profdc9/PicoTheremin/MCTheremin/waves.cpp

#include "waves.h"
const unsigned short sinewave[4096] = {4095,4094,4094,4094,4094,4094,4094,4094,4094,4094,4094,4094,4094,4094,4094,4094,4094,4094,4094,4094,4094,4093,4093,4093,4093,4093,4093,4093,4093,4092,4092,4092,4092,4092,4092,4092,4091,4091,4091,4091,4091,4090,4090,4090,4090,4090,4089,4089,4089,4089,4088,4088,4088,4088,4087,4087,4087,4087,4086,4086,4086,4086,4085,4085,4085,4084,4084,4084,4083,4083,4083,4082,4082,4082,4081,4081,4081,4080,4080,4079,4079,4079,4078,4078,4078,4077,4077,4076,4076,4075,4075,4075,4074,4074,4073,4073,4072,4072,4071,4071,4070,4070,4069,4069,4068,4068,4067,4067,4066,4066,4065,4065,4064,4064,4063,4063,4062,4062,4061,4060,4060,4059,4059,4058,4058,4057,4056,4056,4055,4055,4054,4053,4053,4052,4051,4051,4050,4049,4049,4048,4047,4047,4046,4045,4045,4044,4043,4043,4042,4041,4041,4040,4039,4038,4038,4037,4036,4035,4035,4034,4033,4032,4032,4031,4030,4029,4028,4028,4027,4026,4025,4024,4024,4023,4022,4021,4020,4019,4019,4018,4017,4016,4015,4014,4013,4013,4012,4011,4010,4009,4008,4007,4006,4005,4005,4004,4003,4002,4001,4000,3999,3998,3997,3996,3995,3994,3993,3992,3991,3990,3989,3988,3987,3986,3985,3984,3983,3982,3981,3980,3979,3978,3977,3976,3975,3974,3973,3972,3971,3969,3968,3967,3966,3965,3964,3963,3962,3961,3960,3958,3957,3956,3955,3954,3953,3952,3950,3949,3948,3947,3946,3945,3943,3942,3941,3940,3939,3937,3936,3935,3934,3933,3931,3930,3929,3928,3926,3925,3924,3923,3921,3920,3919,3918,3916,3915,3914,3912,3911,3910,3909,3907,3906,3905,3903,3902,3901,3899,3898,3897,3895,3894,3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
056,4056,4057,4058,4058,4059,4059,4060,4060,4061,4062,4062,4063,4063,4064,4064,4065,4065,4066,4066,4067,4067,4068,4068,4069,4069,4070,4070,4071,4071,4072,4072,4073,4073,4074,4074,4075,4075,4075,4076,4076,4077,4077,4078,4078,4078,4079,4079,4079,4080,4080,4081,4081,4081,4082,4082,4082,4083,4083,4083,4084,4084,4084,4085,4085,4085,4086,4086,4086,4086,4087,4087,4087,4087,4088,4088,4088,4088,4089,4089,4089,4089,4090,4090,4090,4090,4090,4091,4091,4091,4091,4091,4092,4092,4092,4092,4092,4092,4092,4093,4093,4093,4093,4093,4093,4093,4093,4094,4094,4094,4094,4094,4094,4094,4094,4094,4094,4094,4094,4094,4094,4094,4094,4094,4094,4094,4094 };
const unsigned short triangle[4096] = {0,2,4,6,8,10,12,14,16,18,20,22,24,26,28,30,32,34,36,38,40,42,44,46,48,50,52,54,56,58,60,62,64,66,68,70,72,74,76,78,80,82,84,86,88,90,92,94,96,98,100,102,104,106,108,110,112,114,116,118,120,122,124,126,128,130,132,134,136,138,140,142,144,146,148,150,152,154,156,158,160,162,164,166,168,170,172,174,176,178,180,182,184,186,188,190,192,194,196,198,200,202,204,206,208,210,212,214,216,218,220,222,224,226,228,230,232,234,236,238,240,242,244,246,248,250,252,254,256,258,260,262,264,266,268,270,272,274,276,278,280,282,284,286,288,290,292,294,296,298,300,302,304,306,308,310,312,314,316,318,320,322,324,326,328,330,332,334,336,338,340,342,344,346,348,350,352,354,356,358,360,362,364,366,368,370,372,374,376,378,380,382,384,386,388,390,392,394,396,398,400,402,404,406,408,410,412,414,416,418,420,422,424,426,428,430,432,434,436,438,440,442,444,446,448,450,452,454,456,458,460,462,464,466,468,470,472,474,476,478,480,482,484,486,488,490,492,494,496,498,500,502,504,506,508,510,512,514,516,518,520,522,524,526,528,530,532,534,536,538,540,542,544,546,548,550,552,554,556,558,560,562,564,566,568,570,572,574,576,578,580,582,584,586,588,590,592,594,596,598,600,602,604,606,608,610,612,614,616,618,620,622,624,626,628,630,632,634,636,638,640,642,644,646,648,650,652,654,656,658,660,662,664,666,668,670,672,674,676,678,680,682,684,686,688,690,692,694,696,698,700,702,704,706,708,710,712,714,716,718,720,722,724,726,728,730,732,734,736,738,740,742,744,746,748,750,752,754,756,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
const unsigned short *wavelist[4] = {sinewave,triangle,distorted,distorted2};
